torvalds/GuitarPedal/Firmware/exp.h

#ifndef EXP_H
#define EXP_H

//
// The expression jack, as a probe rather than as a feature.
//
// Nothing here is wired into the pedal.  It exists to answer "what is
// actually plugged into that jack, and can we read it well enough to be
// worth having" on a board where the jack has never been used, and it is
// driven entirely by a SysEx request from the host.  When the answer is
// known this wants replacing with something that polls, debounces and
// maps to a pot; until then, guessing at that design would be guessing.
//
// WHAT IS OUT THERE.  Two things, and they want opposite pin setups:
//
//   - a double footswitch, tip and ring each shorting to sleeve.  Wants
//     a pull-up on both pins and a threshold.
//   - an expression pedal, which is a potentiometer on a TRS plug.  Wants
//     one pin driven as the supply and the other read as the wiper.
//
// Expression pedals do not agree on which contact is the wiper.  The
// Roland/Boss convention is ring = supply, tip = wiper; others are the
// other way about.  So this probes *both* polarities rather than picking
// one, and whatever uses it later can decide from the numbers instead of
// from a datasheet nobody has.
//
// WHICH POLARITY, AND WHY IT IS NOT A COIN TOSS.  Measured against a
// Sonicake VEXPRESS, which is Roland-convention - tip = wiper, ring =
// supply, sleeve = the bottom of a nominal 10k pot:
//
//	drive RING -> read TIP      3 .. 3677    span 3674
//	drive TIP  -> read RING      6 .. 3676    span 3670
//
// Both sweep nearly the full range, so "does it move" picks neither.
// The difference is the shape, and it comes straight out of which part
// of the pot the series resistor is loaded by:
//
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
